sparkfun/SparkFun_Portability_Shield/docs/assets/img/27510-Portability-Shield-Action.jpg

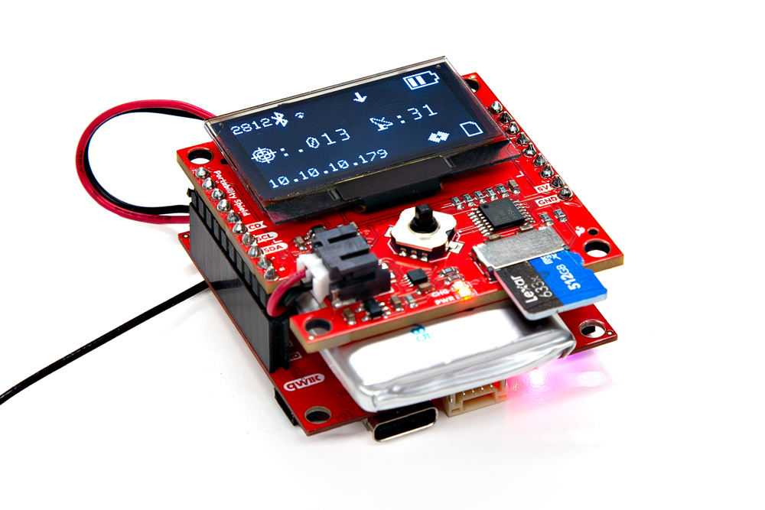
docs/assets/img/27510-Portability-Shield-Action.jpg
