sparkfun/SparkFun_Portability_Shield/docs/assets/img/thumbnail.jpg

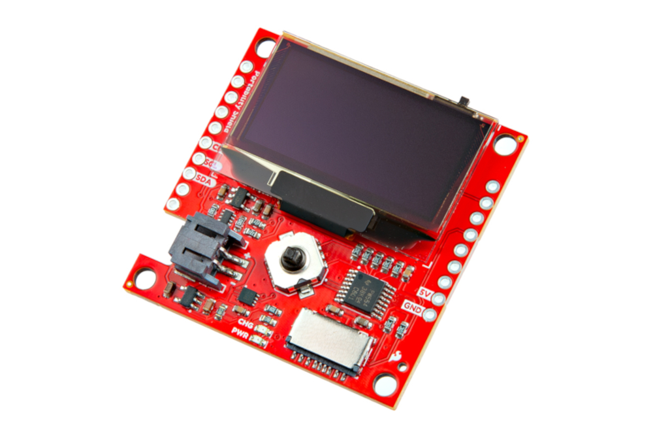
docs/assets/img/thumbnail.jpg
